jcchouinard11/SerreVoRelease/Documentation/OutputReleaseV1SerreVo/SerreVo_Mutliplexeur RG-JCC (PCB Noir - SILK Blanc)/02 - PDF/SerreVo_multiplexeur_SCH REV 1.00.PDF

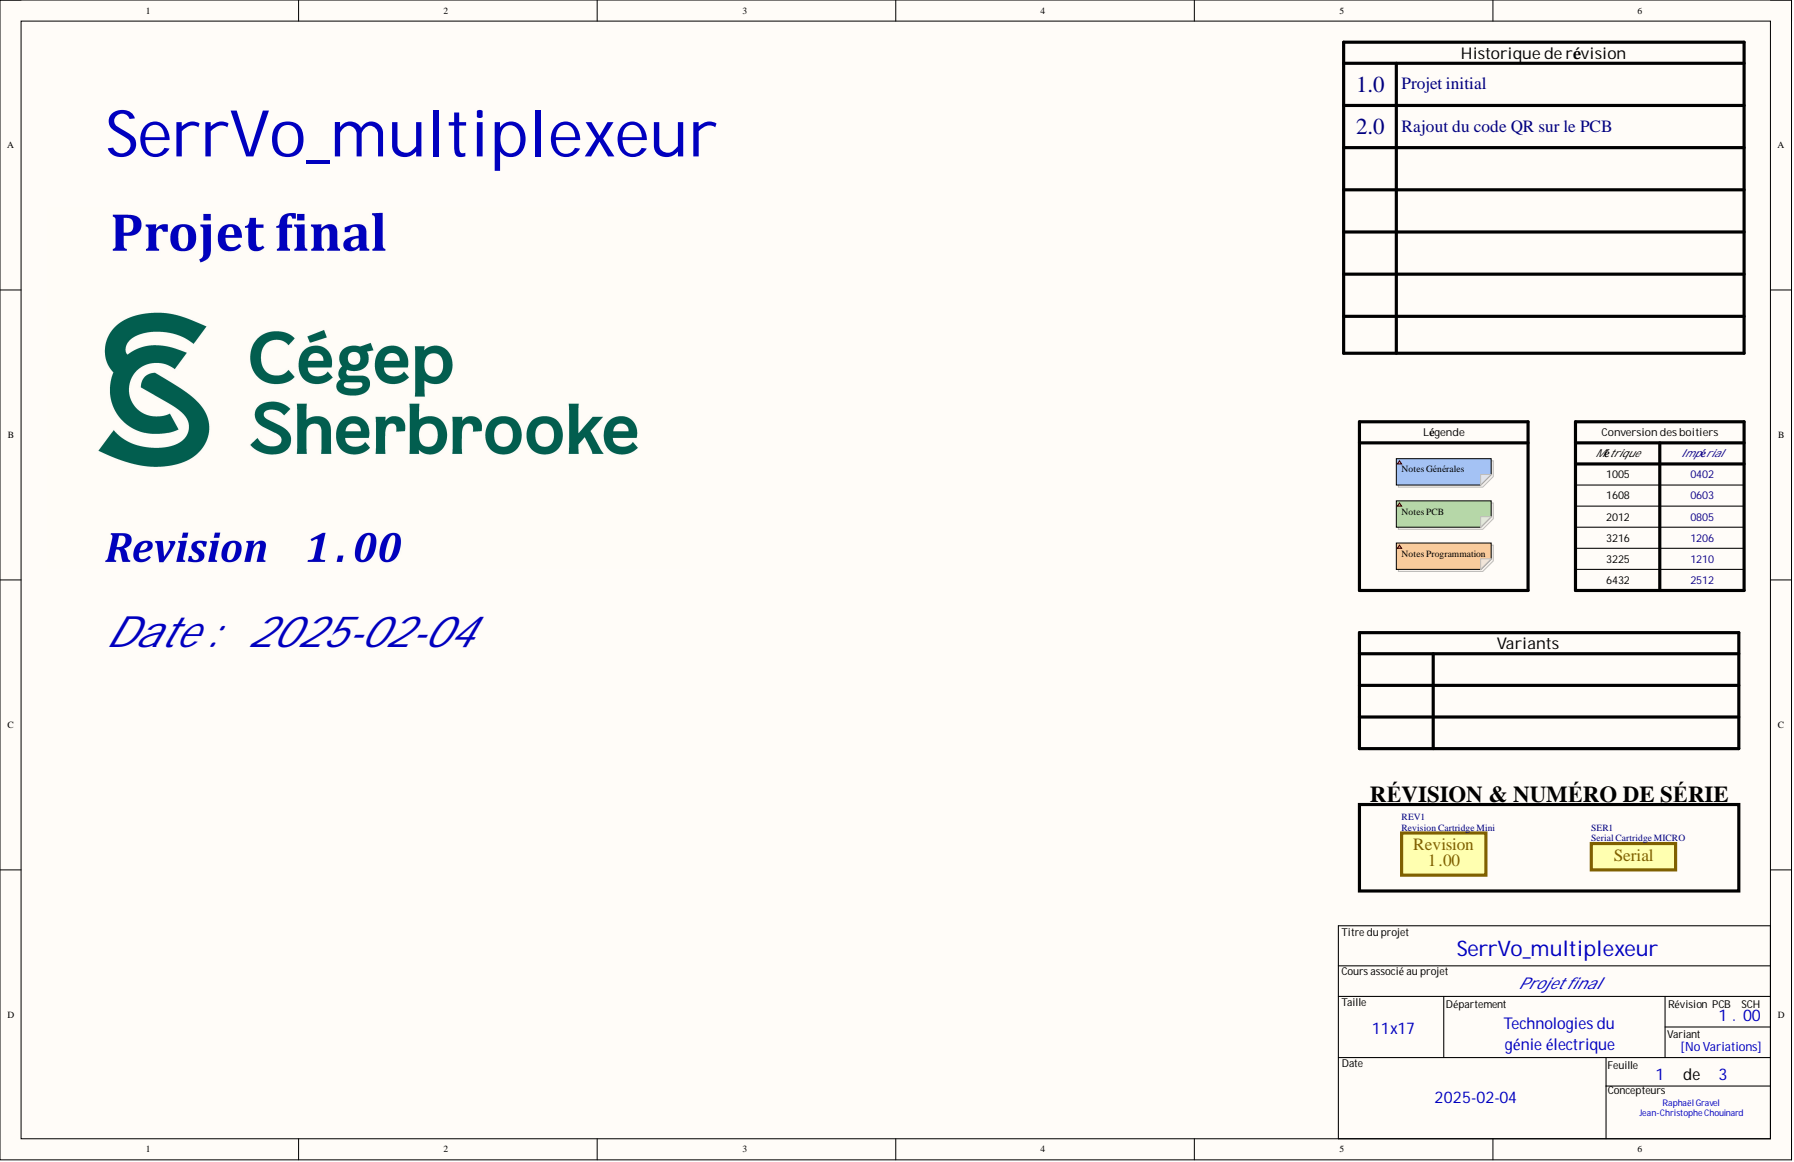
[picture p3: page 1]

1. 0 | Projet initia l

2. 0 | Rajo ut d u co de QR sur le PCB

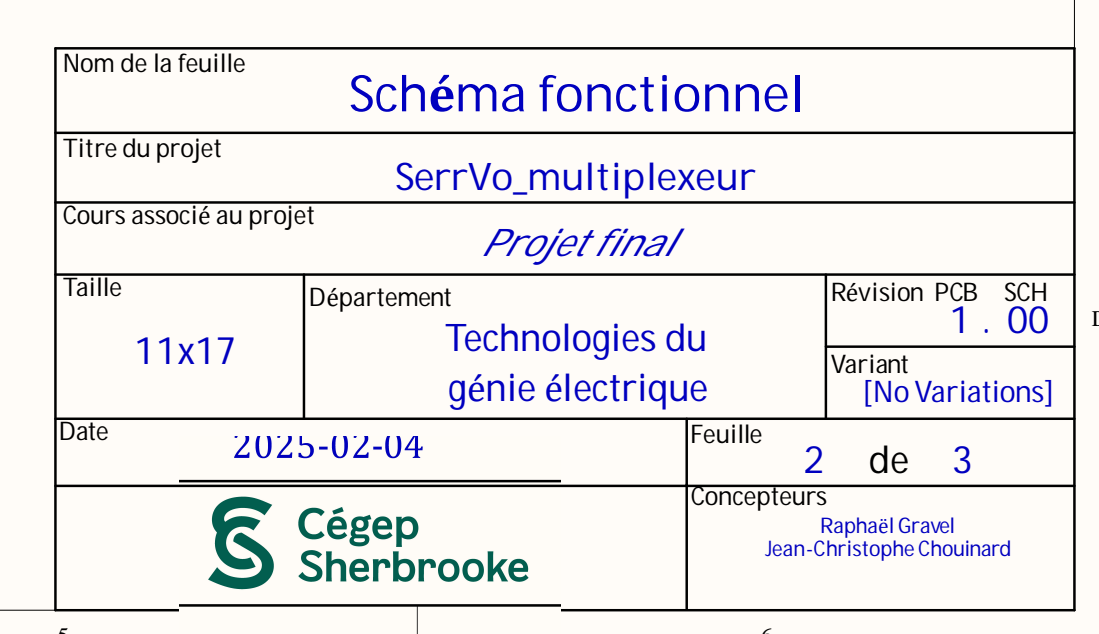
[picture p4: page 2]

Nom de la feuille

Cours associé au projet

Date 2025-02-04 | Feuille 2 de 3

Raphaël Gravel Jean-Christophe Chouinard

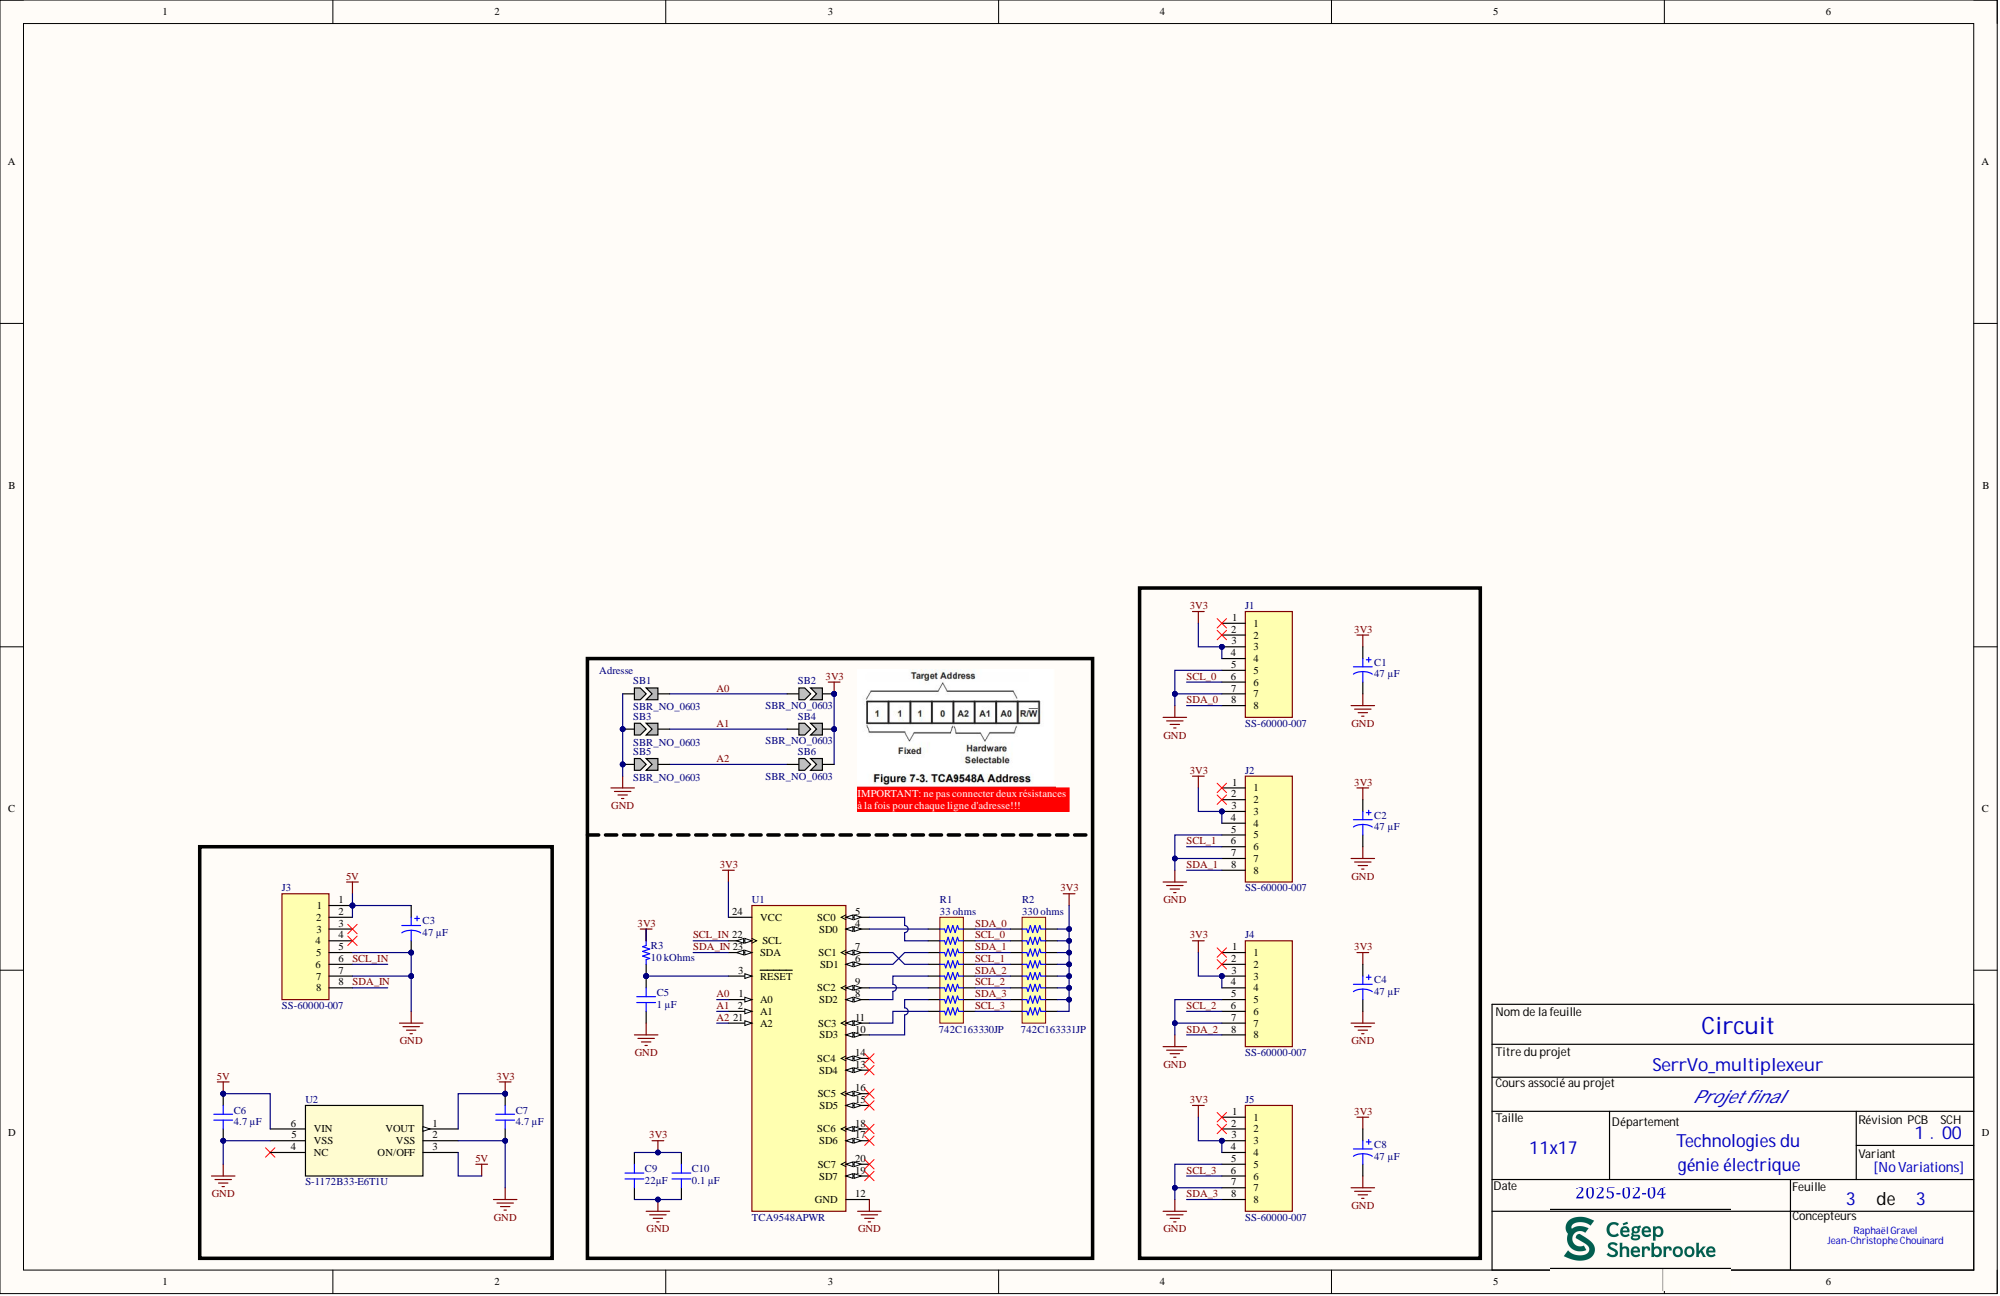
[picture p5: page 3]

Nom de la feui
